jadenvv/NULL/null_elec/OPL_Kicad_Library-master/images/XIAO_Family_2.png

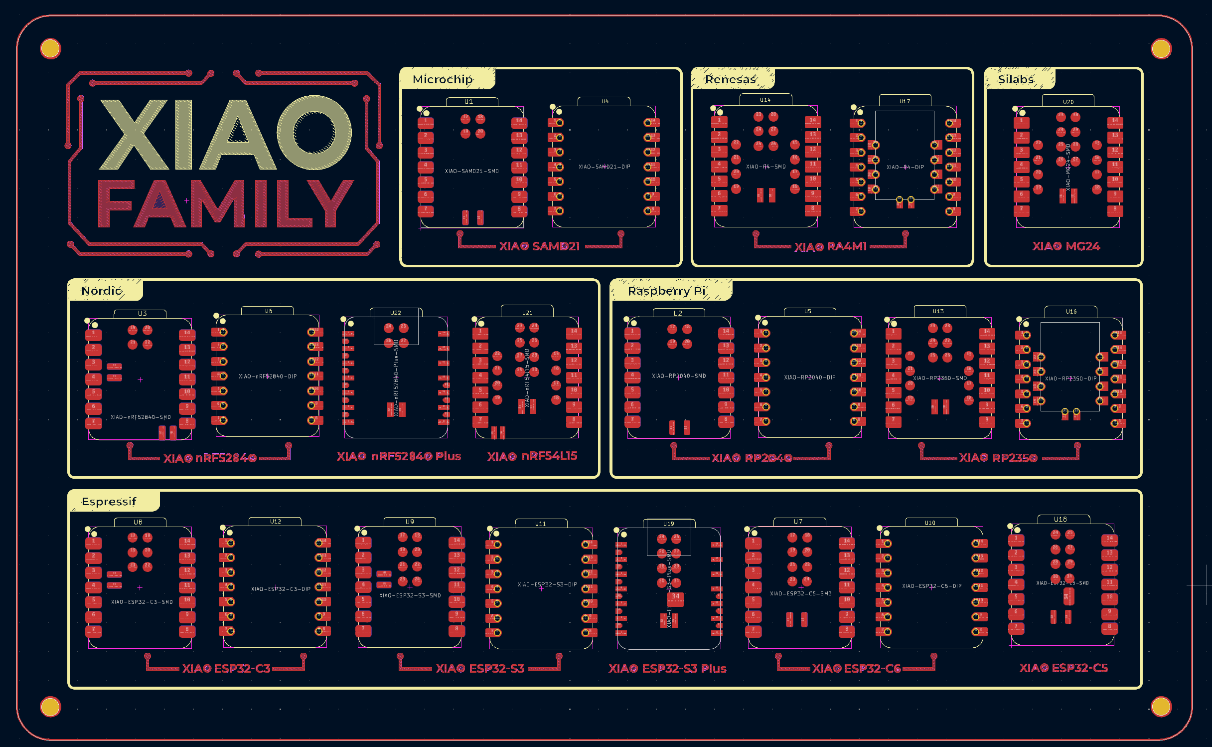
null_elec/OPL_Kicad_Library-master/images/XIAO_Family_2.png
