jadenvv/NULL/null_elec/LIB_TRF7970ARHBR/TRF7970ARHBR/KiCad/NULL.kicad_sch

## KiCad design null_elec/LIB_TRF7970ARHBR/TRF7970ARHBR/KiCad/NULL.kicad_sch (2026-03-05)

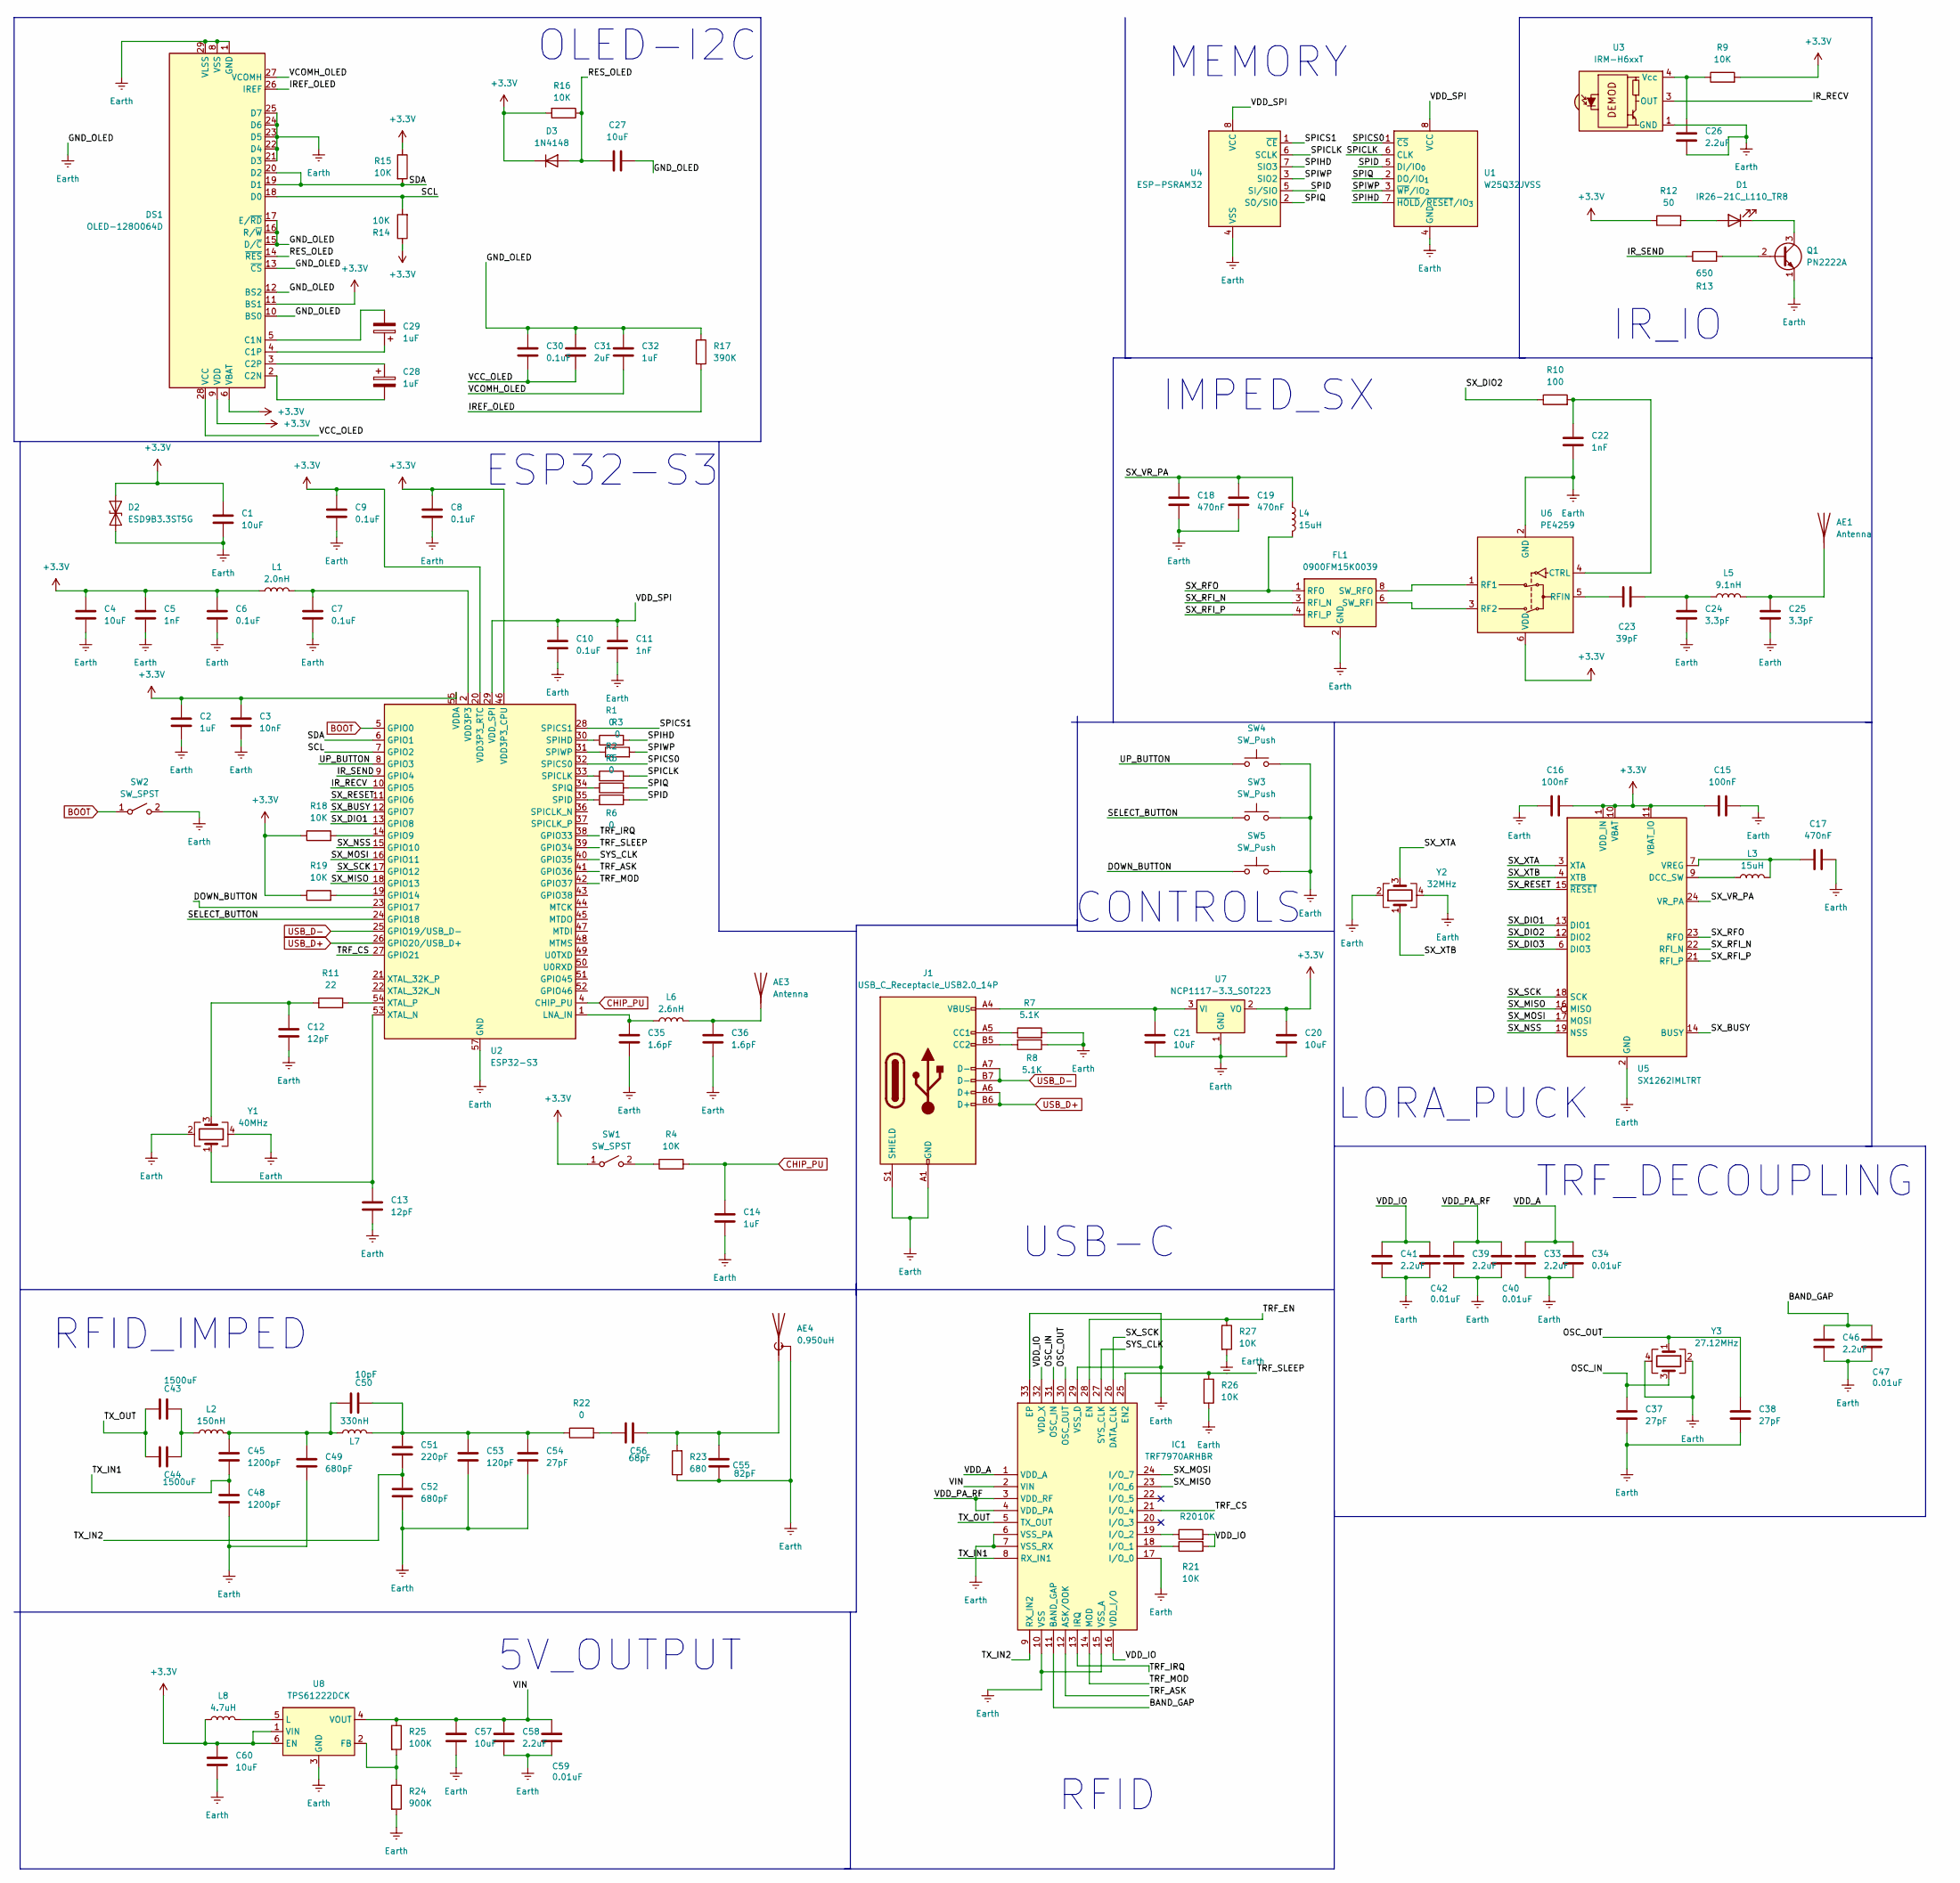
[picture p45: schematic NULL.kicad_sch]

Parts:
AE1: Antenna; PinSocket_1x01_P2.54mm_Vertical
AE3: Antenna; Molex_47948-0001_2.4Ghz
AE4: 0.950uH; Coilcraft_MA5532-AE_RFID
C1, C4, C20, C21, C27, C57, C60: 10uF; C_01005_0402Metric
C2, C14, C28, C29, C32: 1uF; C_01005_0402Metric
C3: 10nF; C_01005_0402Metric
C5, C11, C22: 1nF; C_01005_0402Metric
C6, C7, C8, C9, C10, C30: 0.1uF; C_01005_0402Metric
C12, C13: 12pF; C_01005_0402Metric
C15, C16: 100nF; C_01005_0402Metric
C17, C18, C19: 470nF; C_01005_0402Metric
C23: 39pF; C_01005_0402Metric
C24, C25: 3.3pF; C_01005_0402Metric
C26, C33, C39, C41, C46, C58: 2.2uF; C_01005_0402Metric
C31: 2uF; C_01005_0402Metric
C34, C40, C42, C47, C59: 0.01uF; C_01005_0402Metric
C35, C36: 1.6pF; C_01005_0402Metric
C37, C38, C54: 27pF; C_01005_0402Metric
C43, C44: 1500uF; C_01005_0402Metric
C45, C48: 1200pF; C_01005_0402Metric
C49, C52: 680pF; C_01005_0402Metric
C50: 10pF; C_01005_0402Metric
C51: 220pF; C_01005_0402Metric
C53: 120pF; C_01005_0402Metric
C55: 82pF; C_01005_0402Metric
C56: 68pF; C_01005_0402Metric
D1: IR26-21C_L110_TR8; LED_1206_3216Metric
D2: ESD9B3.3ST5G; D_SOD-923
D3: 1N4148; D_DO-35_SOD27_P7.62mm_Horizontal
DS1: OLED-128O064D
FL1: 0900FM15K0039; Balun_Johanson_0900FM15K0039
IC1: TRF7970ARHBR; QFN50P500X500X100-33N-D; Mouser Part Number 595-TRF7970ARHBR
J1: USB_C_Receptacle_USB2.0_14P; USB_C_Receptacle_GCT_USB4125-xx-x-0190_6P_TopMnt_Horizontal
L1: 2.0nH; L_0402_1005Metric
L2: 150nH; L_0402_1005Metric
L3, L4: 15uH; L_0402_1005Metric
L5: 9.1nH; L_0402_1005Metric
L6: 2.6nH; L_0402_1005Metric
L7: 330nH; L_0402_1005Metric
L8: 4.7uH; L_0402_1005Metric
Q1: PN2222A; TO-92_Inline
R1: 0; L_0402_1005Metric
R2, R3, R5, R6, R22: 0; R_0402_1005Metric
R4, R9, R14, R15, R16, R18, R19, R20, R21, R26, R27: 10K; R_0402_1005Metric
R7, R8: 5.1K; R_0402_1005Metric
R10: 100; R_0402_1005Metric
R11: 22; R_0402_1005Metric
R12: 50; R_0402_1005Metric
R13: 650; R_0402_1005Metric
R17: 390K; R_0402_1005Metric
R23: 680; R_0402_1005Metric
R24: 900K; R_0402_1005Metric
R25: 100K; R_0402_1005Metric
SW1, SW2: SW_SPST
SW3, SW4, SW5: SW_Push; SW_Tactile_SPST_NO_Straight_CK_PTS636Sx25SMTRLFS
U1: W25Q32JVSS; SOIC-8_5.3x5.3mm_P1.27mm
U2: ESP32-S3; QFN-56-1EP_7x7mm_P0.4mm_EP4x4mm
U3: IRM-H6xxT; Everlight_IRM-H6xxT
U4: ESP-PSRAM32; SOIC-8_3.9x4.9mm_P1.27mm
U5: SX1262IMLTRT; QFN-24-1EP_4x4mm_P0.5mm_EP2.6x2.6mm
U6: PE4259; SOT-363_SC-70-6
U7: NCP1117-3.3_SOT223; SOT-223-3_TabPin2
U8: TPS61222DCK; Texas_R-PDSO-G6
Y1: 40MHz; Crystal_SMD_3225-4Pin_3.2x2.5mm
Y2: 32MHz; Crystal_SMD_3225-4Pin_3.2x2.5mm
Y3: 27.12MHz; Crystal_SMD_3225-4Pin_3.2x2.5mm

Connections:
+3.3V: C1.1, C2.1, C3.1, C4.1, C5.1, C6.1, C8.1, C9.1, C15.2, C16.1, C20.1, C60.1, D2.2 (A2), D3.1 (K), DS1.6 (VBAT), DS1.9 (VDD), DS1.11 (BS1), L1.1, L8.1, R9.2, R12.1, R14.1, R15.1, R16.2, R18.1, R19.1, SW1.1 (A), U2.20 (VDD3P3_RTC), U2.46 (VDD3P3_CPU), U2.55 (VDDA), U2.56 (VDDA), U5.1 (VDD_IN), U5.10 (VBAT), U5.11 (VBAT_IO), U6.6 (VDD), U7.2 (VO), U8.1 (VIN), U8.6 (EN)
BAND_GAP: C46.1, C47.1, IC1.11 (BAND_GAP)
BOOT: SW2.1 (A), U2.5 (GPIO0)
CHIP_PU: C14.1, R4.2, U2.4 (CHIP_PU)
DOWN_BUTTON: SW5.1, U2.23 (GPIO17)
Earth: AE4.2 (Shield), C1.2, C2.2, C3.2, C4.2, C5.2, C6.2, C7.2, C8.2, C9.2, C10.2, C11.2, C12.2, C13.2, C14.2, C15.1, C16.2, C17.2, C18.2, C19.2, C20.2, C21.2, C22.2, C24.2, C25.2, C26.2, C27.2, C30.1, C31.1, C32.1, C33.2, C34.2, C35.2, C36.2, C37.2, C38.2, C39.2, C40.2, C41.2, C42.2, C46.2, C47.2, C48.2, C49.2, C52.2, C53.2, C54.2, C55.2, C57.2, C58.2, C59.2, C60.2, D2.1 (A1), DS1.1 (GND), DS1.8 (VSS), DS1.10 (BS0), DS1.12 (BS2), DS1.13 (~CS), DS1.15 (D/~C), DS1.16 (R/~W), DS1.17 (E/~RD), DS1.21 (D3), DS1.22 (D4), DS1.23 (D5), DS1.24 (D6), DS1.25 (D7), DS1.29 (VLSS), DS1.30 (GND), FL1.2 (GND), FL1.5 (GND), FL1.7 (GND), FL1.9 (GND), FL1.10 (GND), IC1.6 (VSS_PA), IC1.7 (VSS_RX), IC1.10 (VSS), IC1.15 (VSS_A), IC1.17 (I/O_0), IC1.29 (VSS_D), IC1.33 (EP), J1.A1 (GND), J1.A12 (GND), J1.B1 (GND), J1.B12 (GND), J1.S1 (SHIELD), Q1.1 (E), R7.2, R8.1, R17.1, R23.1, R24.2, R26.2, R27.2, SW2.2 (B), SW3.2, SW4.2, SW5.2, U1.4 (GND), U2.57 (GND), U3.1 (GND), U3.2 (GND), U4.4 (VSS), U5.2 (GND), U5.5 (GND), U5.8 (GND), U5.20 (GND), U5.25 (GND), U6.2 (GND), U7.1 (GND), U8.3 (GND), Y1.2, Y1.4, Y2.2, Y2.4, Y3.2, Y3.4
IREF_OLED: DS1.26 (IREF), R17.2
IR_RECV: U2.10 (GPIO5), U3.3 (OUT)
IR_SEND: R13.1, U2.9 (GPIO4)
unnamed: AE1.1, C25.1, L5.2
unnamed: AE3.1, C36.1, L6.2
unnamed: AE4.1 (A), C55.1, C56.1, R23.2
unnamed: C7.1, L1.2, U2.2 (VDD3P3), U2.3 (VDD3P3)
unnamed: C12.1, R11.1, Y1.3
unnamed: C13.1, U2.53 (XTAL_N), Y1.1
unnamed: C17.1, L3.2, U5.7 (VREG)
unnamed: C21.1, J1.A4 (VBUS), J1.A9 (VBUS), J1.B4 (VBUS), J1.B9 (VBUS), U7.3 (VI)
unnamed: C22.1, R10.2, U6.4 (CTRL)
unnamed: C23.1, U6.5 (RFIN)
unnamed: C23.2, C24.1, L5.1
unnamed: C26.1, R9.1, U3.4 (Vcc)
unnamed: C28.1, DS1.3 (C2P)
unnamed: C28.2, DS1.2 (C2N)
unnamed: C29.1, DS1.4 (C1P)
unnamed: C29.2, DS1.5 (C1N)
unnamed: C35.1, L6.1, U2.1 (LNA_IN)
unnamed: C43.1, C44.1, L2.1
unnamed: C45.1, C49.1, C50.2, L2.2, L7.1
unnamed: C50.1, C51.1, C53.1, C54.1, L7.2, R22.1
unnamed: C56.2, R22.2
unnamed: D1.1 (K), Q1.3 (C)
unnamed: D1.2 (A), R12.2
unnamed: FL1.6 (SW_RFI), U6.3 (RF2)
unnamed: FL1.8 (SW_RFO), U6.1 (RF1)
unnamed: IC1.18 (I/O_1), R21.1
unnamed: IC1.19 (I/O_2), R20.1
unnamed: J1.A5 (CC1), R7.1
unnamed: J1.B5 (CC2), R8.2
unnamed: L3.1, U5.9 (DCC_SW)
unnamed: L8.2, U8.5 (L)
unnamed: Q1.2 (B), R13.2
unnamed: R1.1, U2.30 (SPIHD)
unnamed: R2.1, U2.33 (SPICLK)
unnamed: R3.1, U2.31 (SPIWP)
unnamed: R4.1, SW1.2 (B)
unnamed: R5.1, U2.34 (SPIQ)
unnamed: R6.2, U2.35 (SPID)
unnamed: R11.2, U2.54 (XTAL_P)
unnamed: R18.2, U2.14 (GPIO9)
unnamed: R19.2, U2.19 (GPIO14)
unnamed: R24.1, R25.2, U8.2 (FB)
OSC_IN: C37.1, IC1.31 (OSC_IN), Y3.3
OSC_OUT: C38.1, IC1.30 (OSC_OUT), Y3.1
RES_OLED: C27.1, D3.2 (A), DS1.14 (~RES), R16.1
SCL: DS1.18 (D0), R14.2, U2.7 (GPIO2)
SDA: DS1.19 (D1), DS1.20 (D2), R15.2, U2.6 (GPIO1)
SELECT_BUTTON: SW3.1, U2.24 (GPIO18)
SPICLK: R2.2, U1.6 (CLK), U4.6 (SCLK)
SPICS0: U1.1 (~CS), U2.32 (SPICS0)
SPICS1: U2.28 (SPICS1), U4.1 (~CE)
SPID: R6.1, U1.5 (DI/IO_{0}), U4.5 (SI/SIO)
SPIHD: R1.2, U1.7 (~HOLD/~RESET/IO_{3}), U4.7 (SIO3)
SPIQ: R5.2, U1.2 (DO/IO_{1}), U4.2 (SO/SIO)
SPIWP: R3.2, U1.3 (~WP/IO_{2}), U4.3 (SIO2)
SX_BUSY: U2.12 (GPIO7), U5.14 (BUSY)
SX_DIO1: U2.13 (GPIO8), U5.13 (DIO1)
SX_DIO2: R10.1, U5.12 (DIO2)
SX_DIO3: U5.6 (DIO3)
SX_MISO: IC1.23 (I/O_6), U2.18 (GPIO13), U5.16 (MISO)
SX_MOSI: IC1.24 (I/O_7), U2.16 (GPIO11), U5.17 (MOSI)
SX_NSS: U2.15 (GPIO10), U5.19 (NSS)
SX_RESET: U2.11 (GPIO6), U5.15 (~RESET)
SX_RFI_N: FL1.3 (RFI_N), U5.22 (RFI_N)
SX_RFI_P: FL1.4 (RFI_P), U5.21 (RFI_P)
SX_RFO: FL1.1 (RFO), L4.2, U5.23 (RFO)
SX_SCK: IC1.26 (DATA_CLK), U2.17 (GPIO12), U5.18 (SCK)
SX_VR_PA: C18.1, C19.1, L4.1, U5.24 (VR_PA)
SX_XTA: U5.3 (XTA), Y2.3
SX_XTB: U5.4 (XTB), Y2.1
SYS_CLK: IC1.27 (SYS_CLK), U2.40 (GPIO35)
TRF_ASK: IC1.12 (ASK/OOK), U2.41 (GPIO36)
TRF_CS: IC1.21 (I/O_4), U2.27 (GPIO21)
TRF_EN: IC1.28 (EN), R27.1
TRF_IRQ: IC1.13 (IRQ), U2.38 (GPIO33)
TRF_MOD: IC1.14 (MOD), U2.42 (GPIO37)
TRF_SLEEP: IC1.25 (EN2), R26.1, U2.39 (GPIO34)
TX_IN1: C45.2, C48.1, IC1.8 (RX_IN1)
TX_IN2: C51.2, C52.1, IC1.9 (RX_IN2)
TX_OUT: C43.2, C44.2, IC1.5 (TX_OUT)
UP_BUTTON: SW4.1, U2.8 (GPIO3)
USB_D+: J1.A6 (D+), J1.B6 (D+), U2.26 (GPIO20/USB_D+)
USB_D-: J1.A7 (D-), J1.B7 (D-), U2.25 (GPIO19/USB_D-)
VCC_OLED: C30.2, C31.2, DS1.28 (VCC)
VCOMH_OLED: C32.2, DS1.27 (VCOMH)
VDD_A: C33.1, C34.1, IC1.1 (VDD_A)
VDD_IO: C41.1, C42.1, IC1.16 (VDD_I/O), IC1.32 (VDD_X), R20.2, R21.2
VDD_PA_RF: C39.1, C40.1, IC1.3 (VDD_RF), IC1.4 (VDD_PA)
VDD_SPI: C10.1, C11.1, U1.8 (VCC), U2.29 (VDD_SPI), U4.8 (VCC)
VIN: C57.1, C58.1, C59.1, IC1.2 (VIN), R25.1, U8.4 (VOUT)

Notes on the sheet:
TRF_DECOUPLING
MEMORY
LORA_PUCK
5V_OUTPUT
CONTROLS
RFID_IMPED
OLED-I2C
RFID
IR_IO
ESP32-S3
IMPED_SX
USB-C
